Clem-a-la-gome/TheGotitaProject_YI2023/webapp/src/images/img1.png

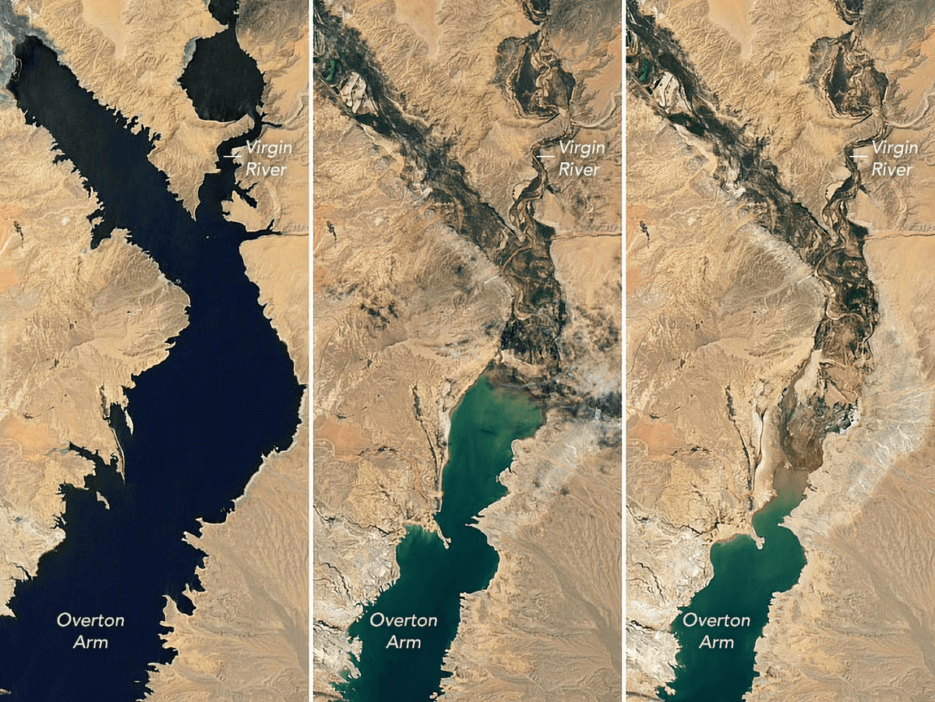
webapp/src/images/img1.png
