Clem-a-la-gome/TheGotitaProject_YI2023/webapp/src/images/img3.jpg

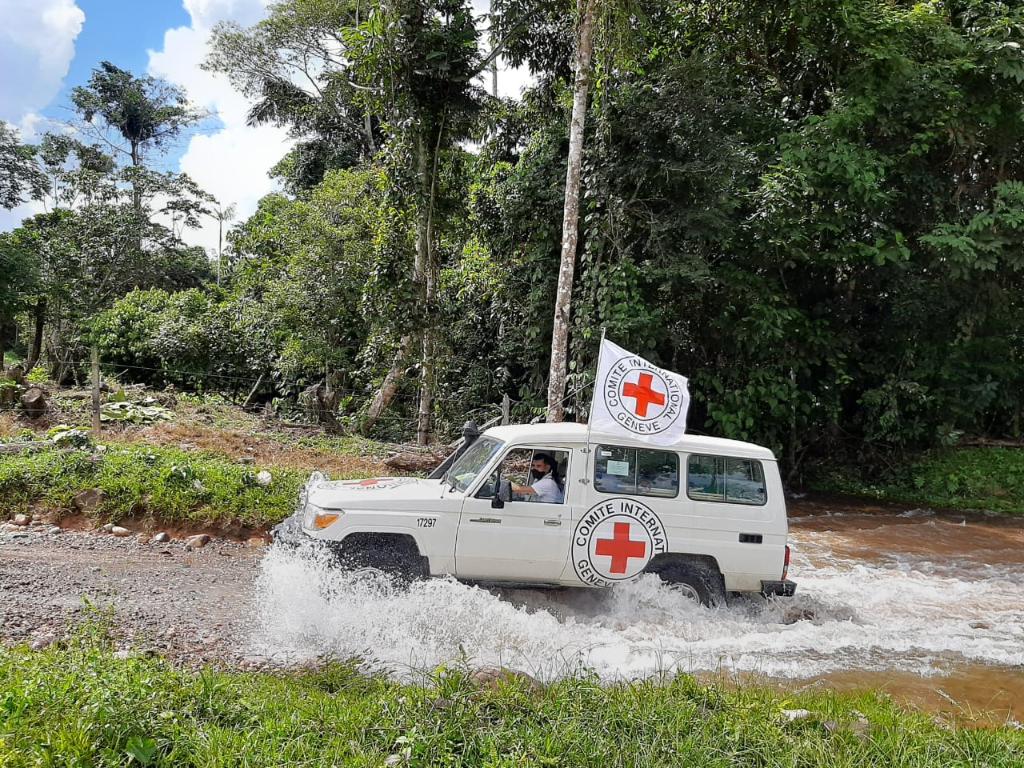
webapp/src/images/img3.jpg
