Clem-a-la-gome/TheGotitaProject_YI2023/webapp/src/images/img6.jpg

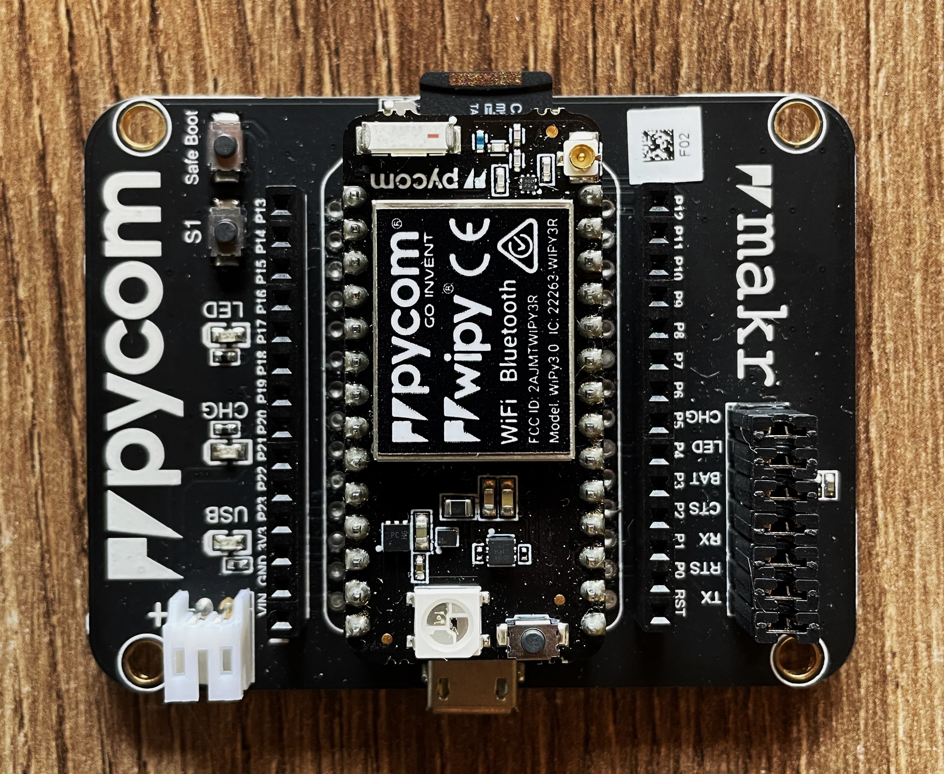
webapp/src/images/img6.jpg
