Clem-a-la-gome/TheGotitaProject_YI2023/webapp/src/images/img6_sup.png

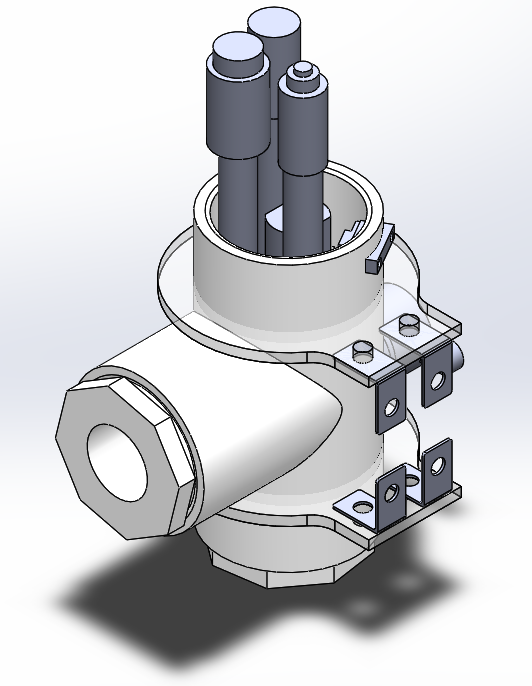
webapp/src/images/img6_sup.png
