Clem-a-la-gome/TheGotitaProject_YI2023/webapp/src/images/tgp1.jpg

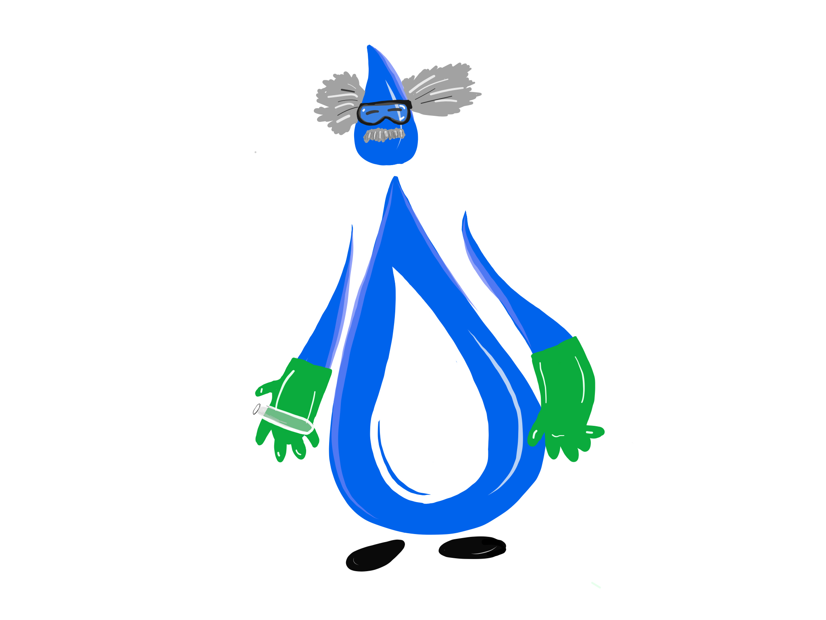
webapp/src/images/tgp1.jpg
