Clem-a-la-gome/TheGotitaProject_YI2023/cad/CAD_1V/electronics/motor.SLDPRT

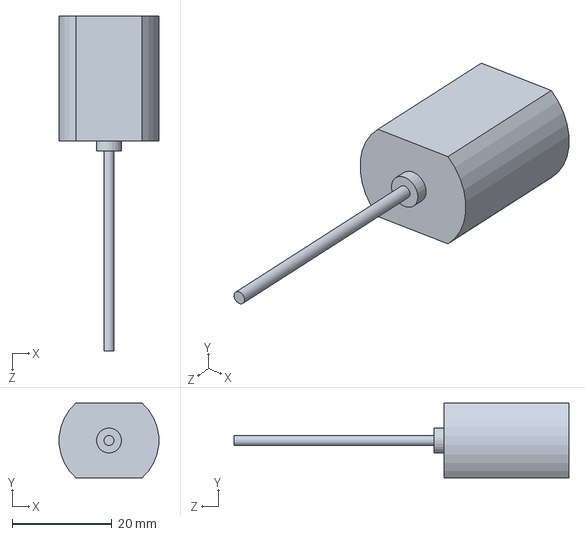
[picture p35: CAD file, 2023-07-28]
cad/CAD_1V/electronics/motor.SLDPRT
19.9 x 15.0 x 67.0 mm
