Clem-a-la-gome/TheGotitaProject_YI2023/cad/CAD_1V/pipeline_connection/niple.SLDPRT

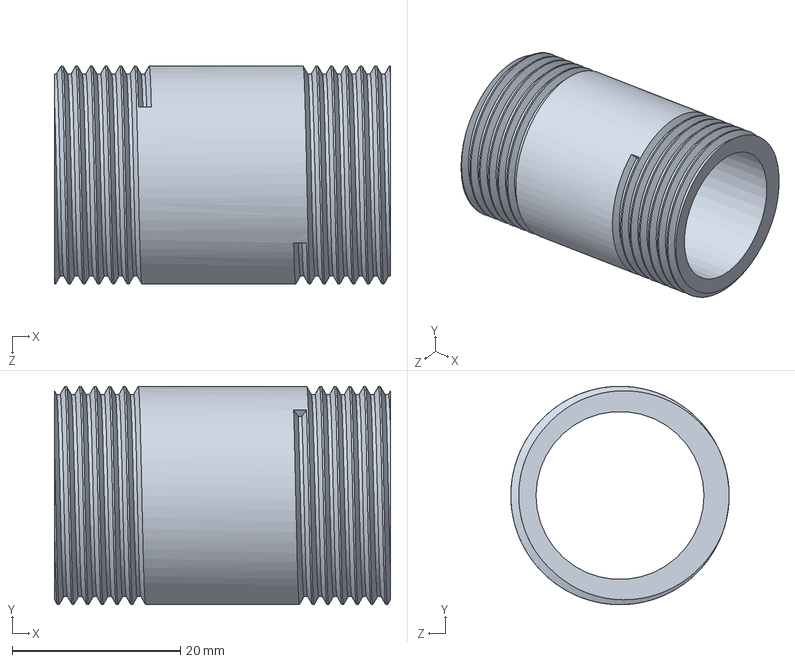
[picture p36: CAD file, 2023-07-28]
cad/CAD_1V/pipeline_connection/niple.SLDPRT
40.0 x 26.0 x 26.0 mm
