Clem-a-la-gome/TheGotitaProject_YI2023/cad/CAD_1V/acrilyc/reducing_ring_4mm_d26mm.SLDPRT

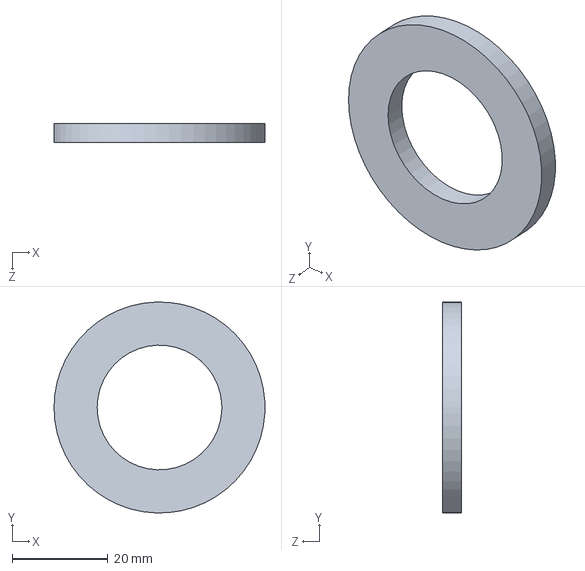
[picture p37: CAD file, 2023-07-28]
cad/CAD_1V/acrilyc/reducing_ring_4mm_d26mm.SLDPRT
44.0 x 44.0 x 4.00 mm
