Clem-a-la-gome/TheGotitaProject_YI2023/cad/CAD_1V/electronics/Gravity Turbidity Sensor.SLDPRT

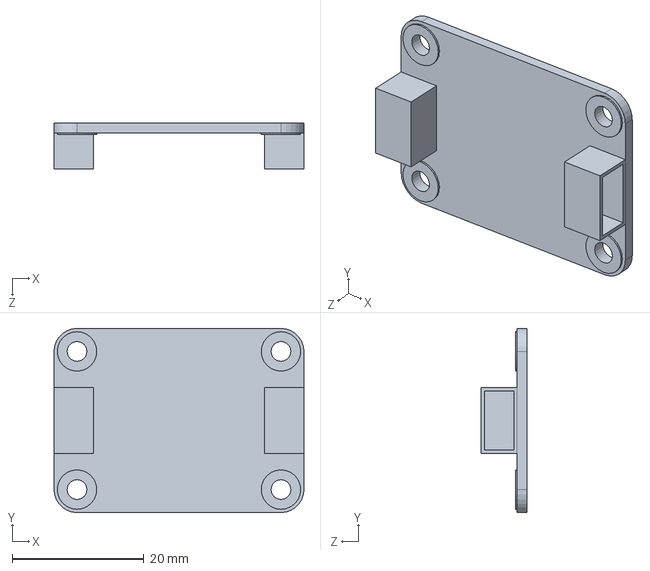
[picture p38: CAD file, 2023-07-28]
cad/CAD_1V/electronics/Gravity Turbidity Sensor.SLDPRT
38.0 x 28.0 x 7.00 mm
