Clem-a-la-gome/TheGotitaProject_YI2023/cad/CAD_1V/pipeline_connection/DS18B20.stp.SLDPRT

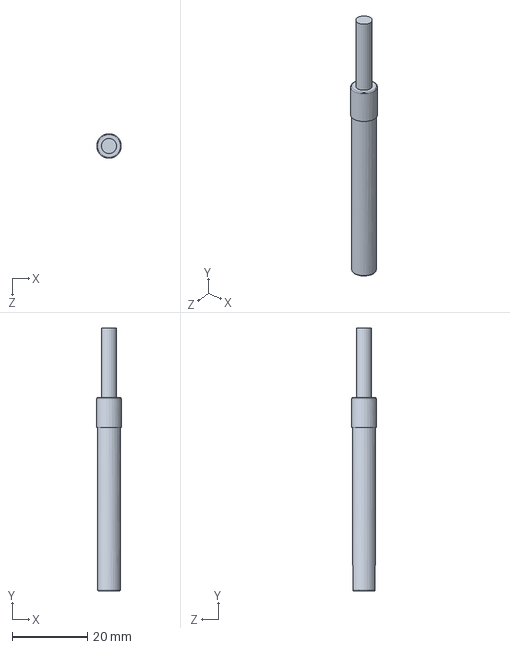
[picture p39: CAD file, 2023-07-28]
cad/CAD_1V/pipeline_connection/DS18B20.stp.SLDPRT
6.50 x 69.7 x 6.50 mm
