Clem-a-la-gome/TheGotitaProject_YI2023/cad/CAD_1V/acrilyc/sensors_support_1.SLDPRT

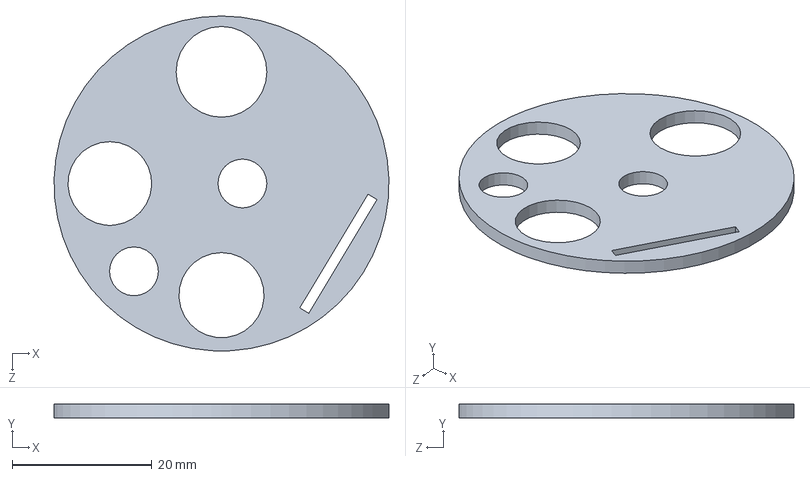
[picture p40: CAD file, 2023-07-28]
cad/CAD_1V/acrilyc/sensors_support_1.SLDPRT
48.0 x 2.00 x 48.0 mm
