Clem-a-la-gome/TheGotitaProject_YI2023/cad/CAD_1V/electronics/do_electrode.SLDPRT

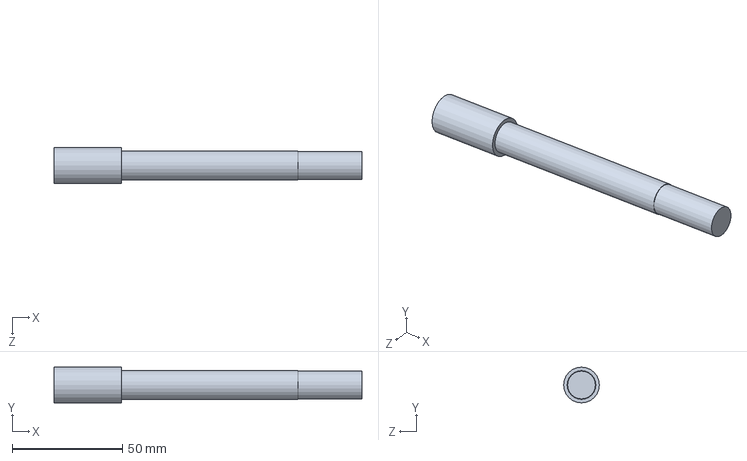
[picture p41: CAD file, 2023-07-28]
cad/CAD_1V/electronics/do_electrode.SLDPRT
139.5 x 16.2 x 16.2 mm
