Clem-a-la-gome/TheGotitaProject_YI2023/cad/CAD_1V/pipeline_connection/ball_valve_part1.SLDPRT

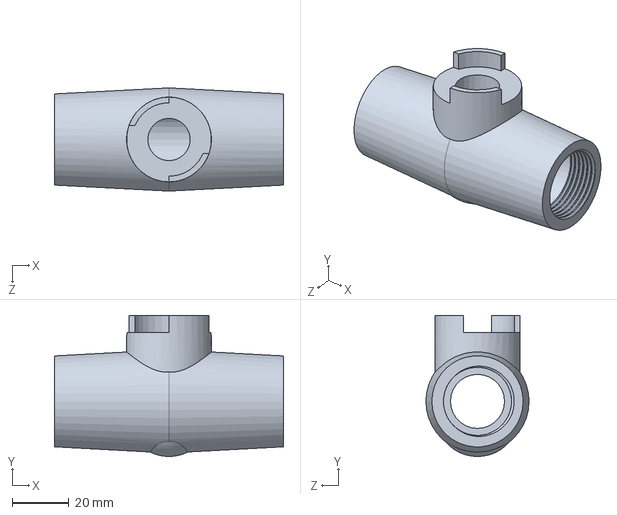
[picture p42: CAD file, 2023-07-28]
cad/CAD_1V/pipeline_connection/ball_valve_part1.SLDPRT
81.0 x 49.9 x 36.5 mm
