Clem-a-la-gome/TheGotitaProject_YI2023/cad/CAD_1V/acrilyc/t_supports.SLDPRT

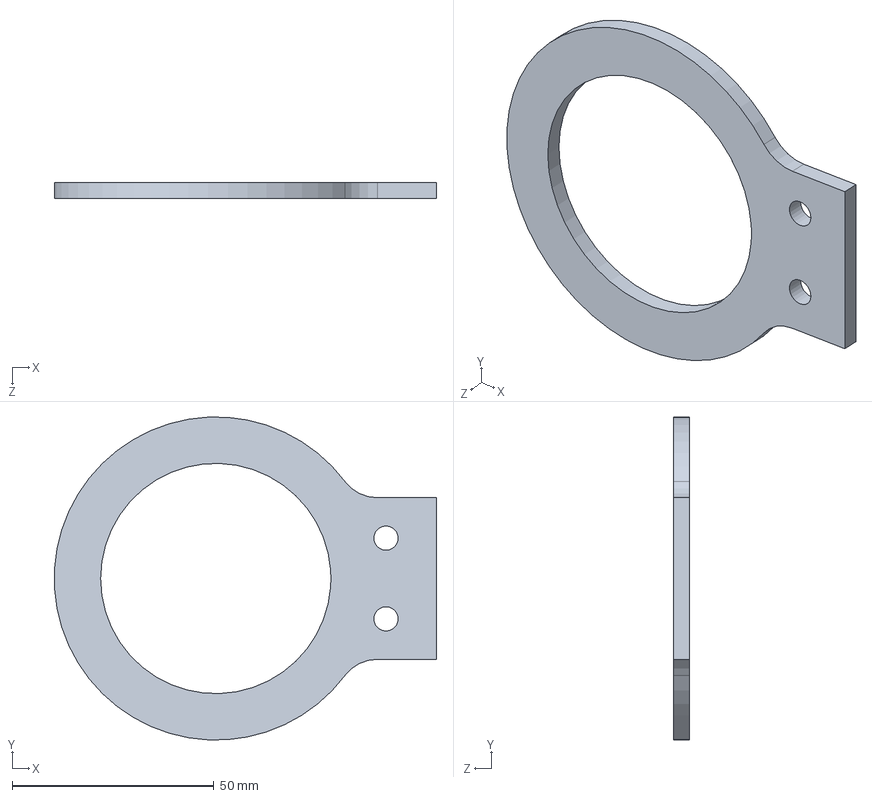
[picture p43: CAD file, 2023-07-28]
cad/CAD_1V/acrilyc/t_supports.SLDPRT
94.6 x 79.9 x 4.00 mm
