Clem-a-la-gome/TheGotitaProject_YI2023/cad/CAD_1V/pipeline_connection/electrovalvula.SLDPRT

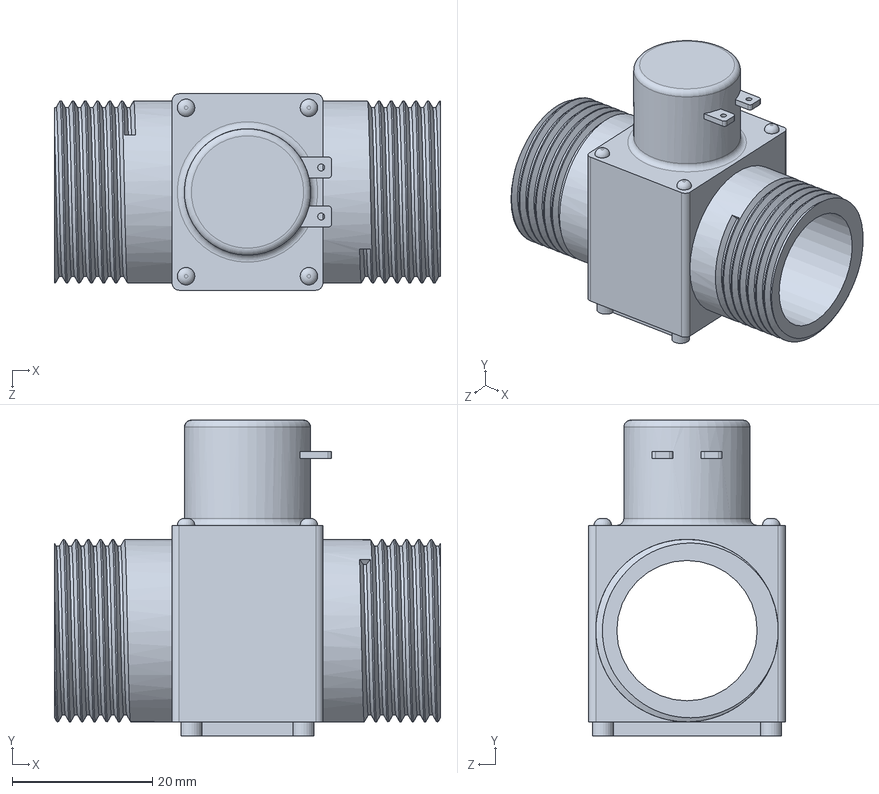
[picture p44: CAD file, 2023-07-28]
cad/CAD_1V/pipeline_connection/electrovalvula.SLDPRT
55.0 x 45.0 x 28.0 mm
