Clem-a-la-gome/TheGotitaProject_YI2023/cad/CAD_1V/electronics/support.SLDPRT

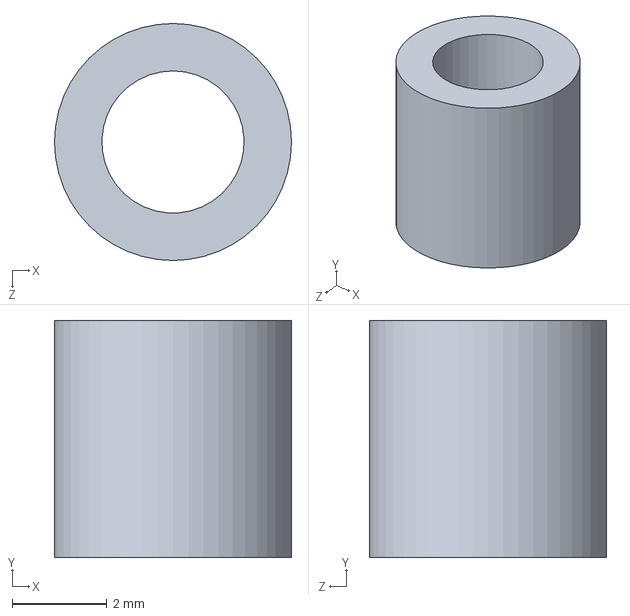
[picture p45: CAD file, 2023-07-28]
cad/CAD_1V/electronics/support.SLDPRT
5.00 x 5.00 x 5.00 mm
