Clem-a-la-gome/TheGotitaProject_YI2023/cad/CAD_1V/electronics/pH_electrode.SLDPRT

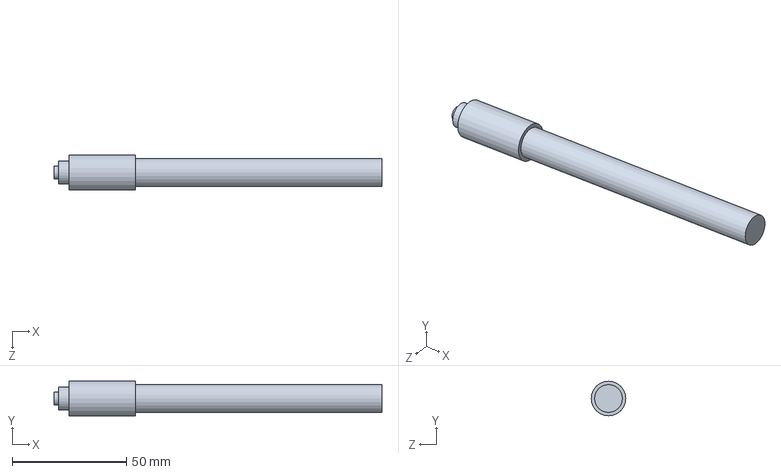
[picture p46: CAD file, 2023-07-28]
cad/CAD_1V/electronics/pH_electrode.SLDPRT
143.7 x 15.2 x 15.2 mm
