Clem-a-la-gome/TheGotitaProject_YI2023/cad/CAD_1V/electronics/Antenna90deg.SLDPRT

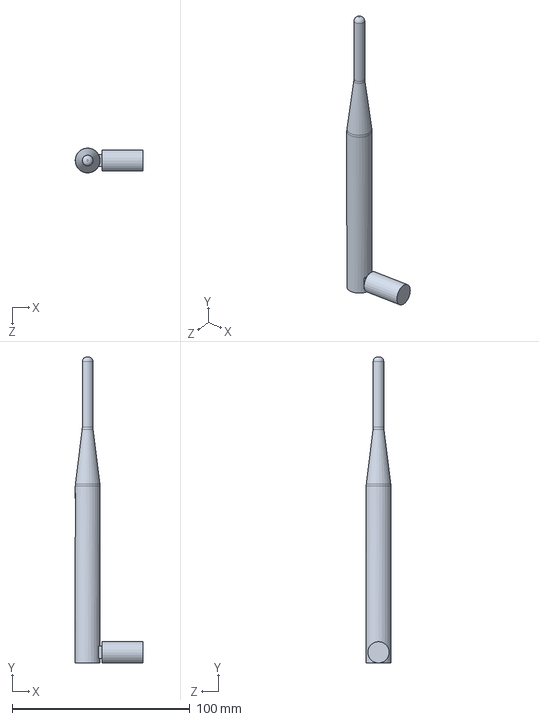
[picture p47: CAD file, 2023-07-28]
cad/CAD_1V/electronics/Antenna90deg.SLDPRT
38.0 x 172.0 x 14.0 mm
