Clem-a-la-gome/TheGotitaProject_YI2023/cad/CAD_1V/electronics/pycom_box.SLDPRT

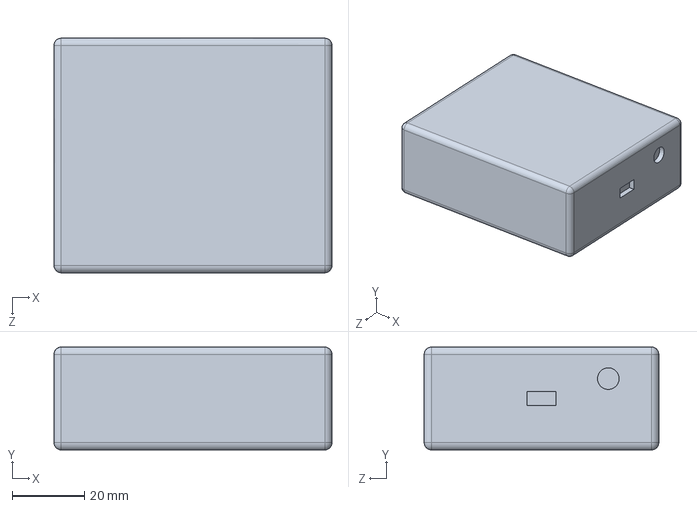
[picture p48: CAD file, 2023-07-28]
cad/CAD_1V/electronics/pycom_box.SLDPRT
77.0 x 28.5 x 65.0 mm
