Clem-a-la-gome/TheGotitaProject_YI2023/cad/CAD_1V/electronics/Relay - 2 Channel - 2PH63091A.SLDPRT

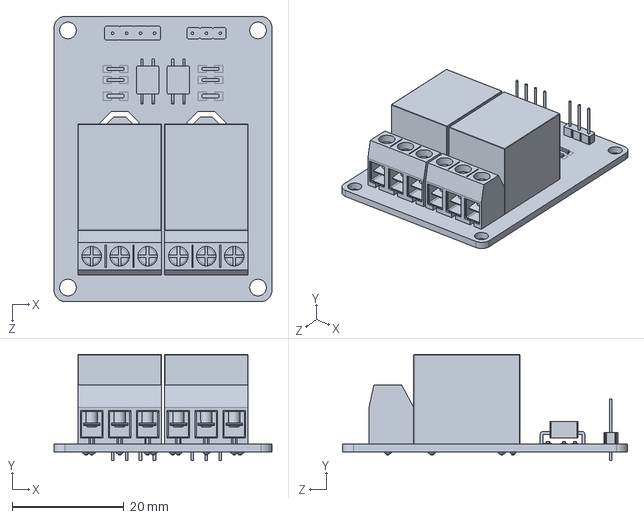
[picture p49: CAD file, 2023-07-28]
cad/CAD_1V/electronics/Relay - 2 Channel - 2PH63091A.SLDPRT
39.0 x 19.0 x 51.0 mm
