Clem-a-la-gome/TheGotitaProject_YI2023/cad/CAD_1V/electronics/ec_electrode.SLDPRT

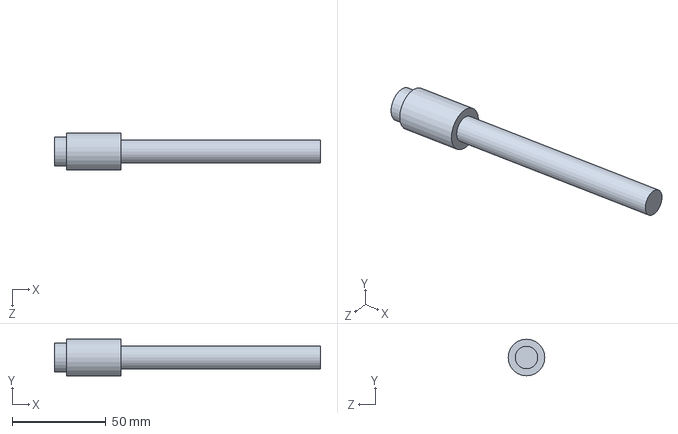
[picture p50: CAD file, 2023-07-28]
cad/CAD_1V/electronics/ec_electrode.SLDPRT
141.5 x 19.5 x 19.5 mm
