Clem-a-la-gome/TheGotitaProject_YI2023/cad/CAD_1V/electronics/turbidity_sensor.SLDPRT

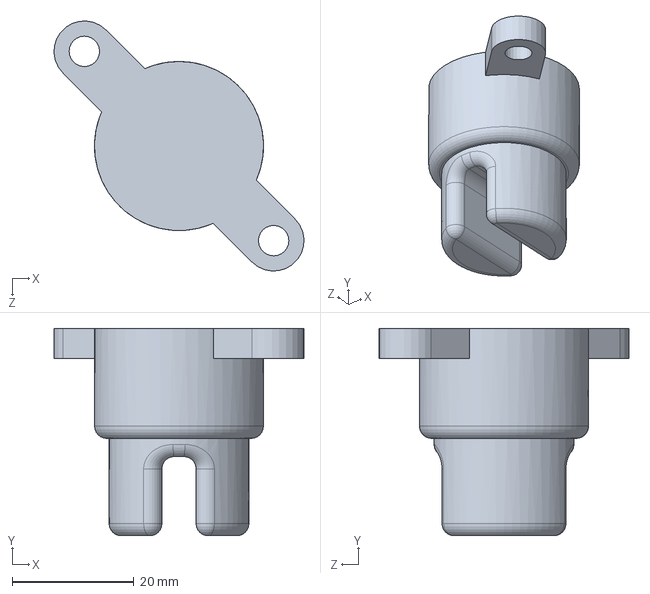
[picture p51: CAD file, 2023-07-28]
cad/CAD_1V/electronics/turbidity_sensor.SLDPRT
41.1 x 34.1 x 41.1 mm
