Clem-a-la-gome/TheGotitaProject_YI2023/cad/CAD_1V/electronics/level_sensor.SLDPRT

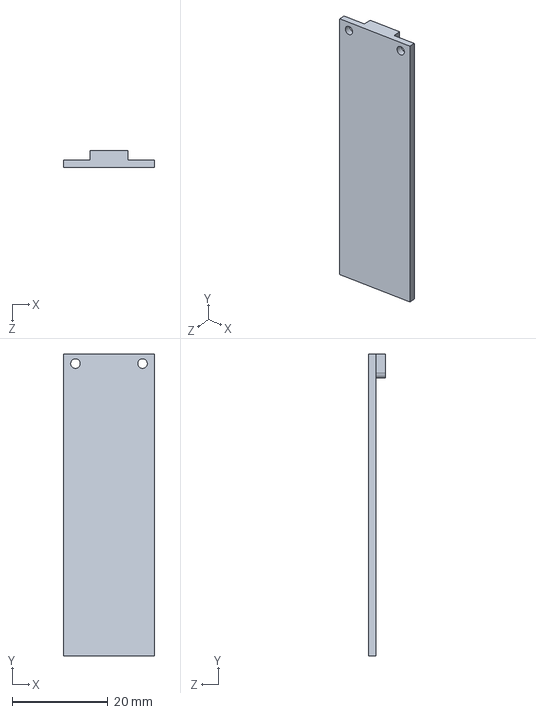
[picture p52: CAD file, 2023-07-28]
cad/CAD_1V/electronics/level_sensor.SLDPRT
19.0 x 63.0 x 3.50 mm
